ethmacc/CASA0022_TerRanger/Data/logs/Screenshot 2025-06-04 141134.png

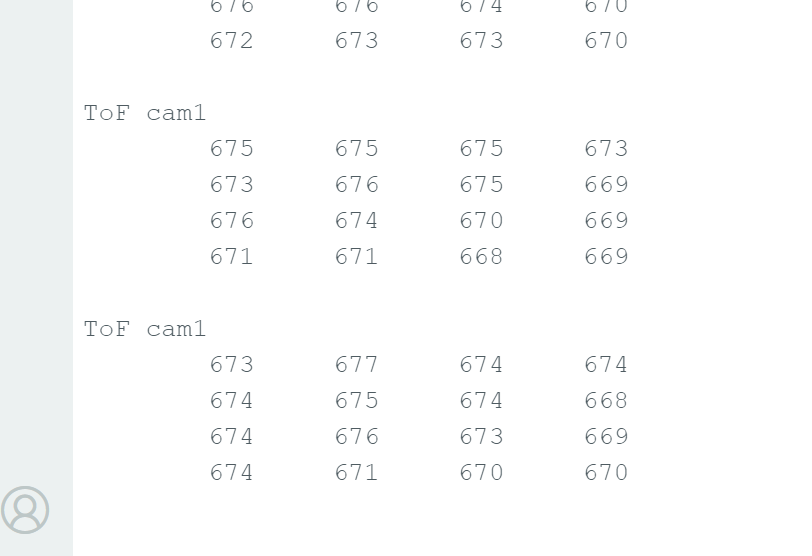
Data/logs/Screenshot 2025-06-04 141134.png
